modtronix-com/esp32MX-E/images/esp32mx-e_with_proto_db_back.jpg

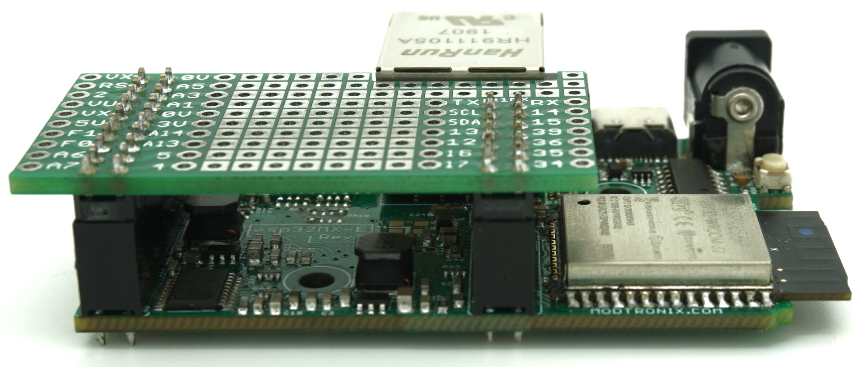
images/esp32mx-e_with_proto_db_back.jpg
