modtronix-com/esp32MX-E/images/esp32mx-e_with_proto_db_front.jpg

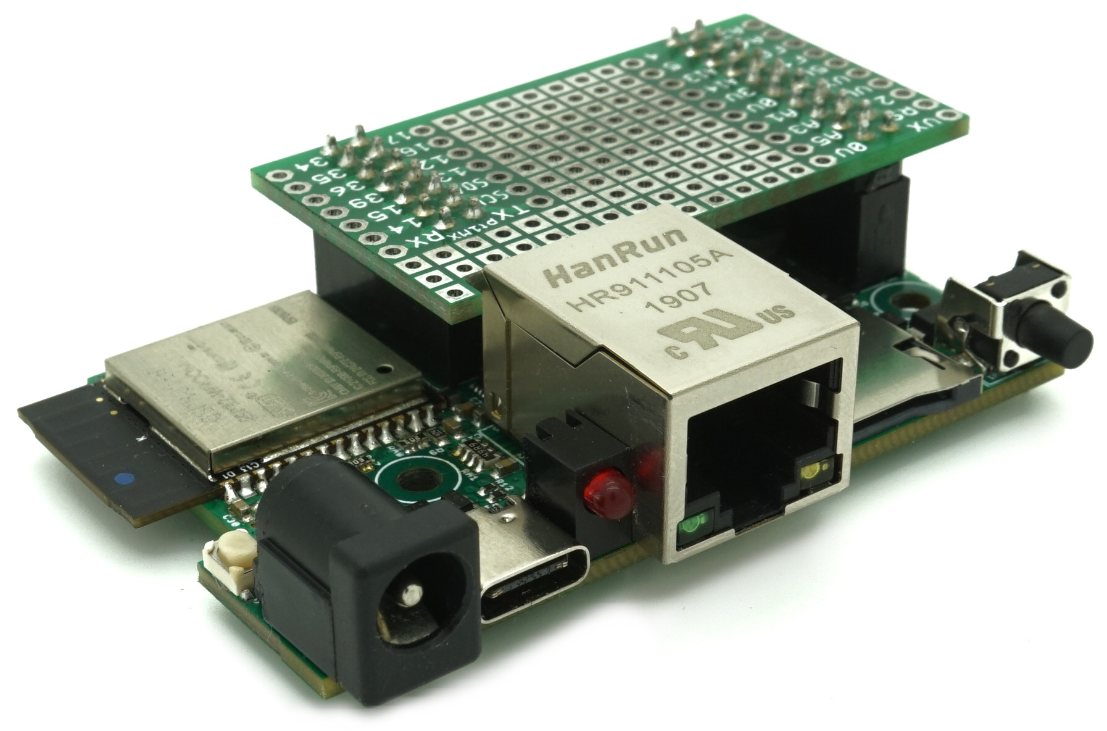
images/esp32mx-e_with_proto_db_front.jpg
