modtronix-com/esp32MX-E/pcb/pt1mx/pt1mx_schematics.png

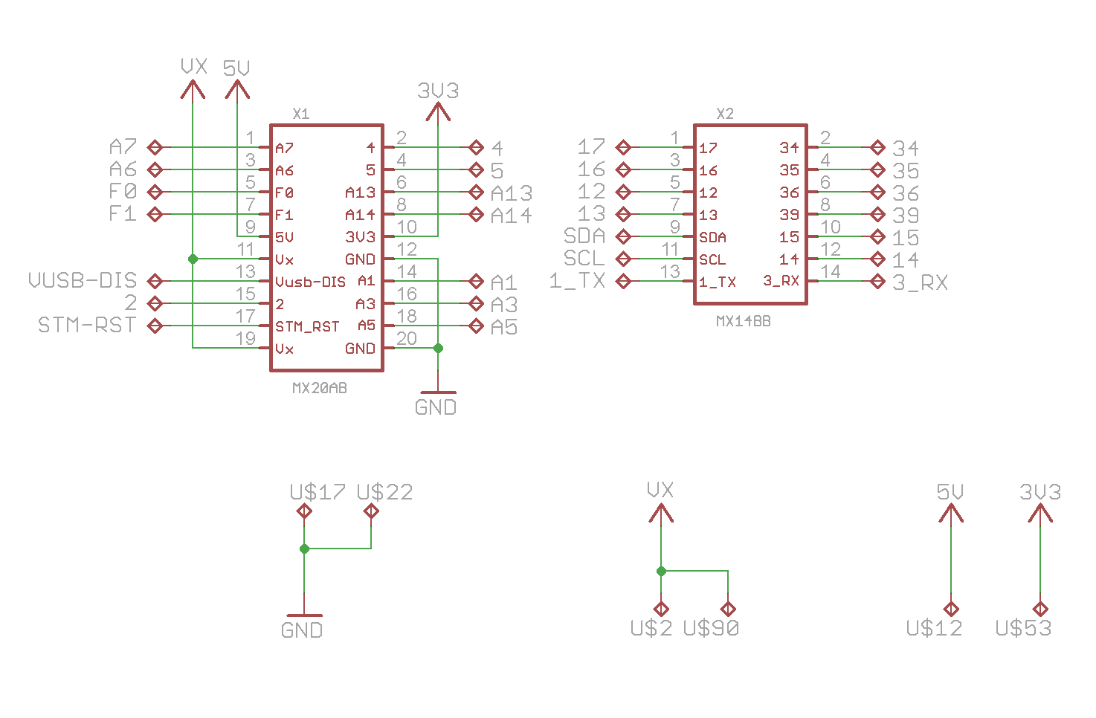
pcb/pt1mx/pt1mx_schematics.png
