modtronix-com/esp32MX-E/examples/idf/ethernet/main/main.c

/* ethernet Example

   This example code is in the Public Domain (or CC0 licensed, at your option.)

   Unless required by applicable law or agreed to in writing, this
   software is distributed on an "AS IS" BASIS, WITHOUT WARRANTIES OR
   CONDITIONS OF ANY KIND, either express or implied.
*/
#include <stdio.h>
#include <string.h>
#include "freertos/FreeRTOS.h"
#include "freertos/task.h"
#include "driver/gpio.h"
#include "tcpip_adapter.h"
#include "esp_eth.h"
#include "esp_event.h"
#include "esp_log.h"
#include "sdkconfig.h"


///////////////////////////////////////////////////////////////////////////////
// Defines
///////////////////////////////////////////////////////////////////////////////

#define BLINK_GPIO 5	// esp32MX-E uses GPIO 5 for the LED
// TODO: Chage to use CONFIG_ESP32MX_LED_GPIO as set by menuconfig

// Used when DHCP server is disabled
#define IP_DEFAULT_ADDRESS		"10.1.0.240"
#define IP_DEFAULT_NETMASK      "255.255.255.0"
#define IP_DEFAULT_GATEWAY      "10.1.0.254"

static const char *TAG = "eth_example";

/** Event handler for Ethernet events */
static void eth_event_handler(void *arg, esp_event_base_t event_base, int32_t event_id, void *event_data)
{
    uint8_t mac_addr[6] = {0};
    /* we can get the ethernet driver handle from event data */
    esp_eth_handle_t eth_handle = *(esp_eth_handle_t *)event_data;

    switch (event_id) {
    case ETHERNET_EVENT_CONNECTED:
        esp_eth_ioctl(eth_handle, ETH_CMD_G_MAC_ADDR, mac_addr);
        ESP_LOGI(TAG, "Ethernet Link Up");
        ESP_LOGI(TAG, "Ethernet HW Addr %02x:%02x:%02x:%02x:%02x:%02x",
                 mac_addr[0], mac_addr[1], mac_addr[2], mac_addr[3], mac_addr[4], mac_addr[5]);
        break;
    case ETHERNET_EVENT_DISCONNECTED:
        ESP_LOGI(TAG, "Ethernet Link Down");
        break;
    case ETHERNET_EVENT_START:
        ESP_LOGI(TAG, "Ethernet Started");
        break;
    case ETHERNET_EVENT_STOP:
        ESP_LOGI(TAG, "Ethernet Stopped");
        break;
    default:
        break;
    }
}

/** Event handler for IP_EVENT_ETH_GOT_IP */
static void got_ip_event_handler(void *arg, esp_event_base_t event_base, int32_t event_id, void *event_data)
{
    ip_event_got_ip_t *event = (ip_event_got_ip_t *) event_data;
    const tcpip_adapter_ip_info_t *ip_info = &event->ip_info;

    ESP_LOGI(TAG, "Ethernet Got IP Address");
    ESP_LOGI(TAG, "~~~~~~~~~~~");
    ESP_LOGI(TAG, "ETHIP:" IPSTR, IP2STR(&ip_info->ip));
    ESP_LOGI(TAG, "ETHMASK:" IPSTR, IP2STR(&ip_info->netmask));
    ESP_LOGI(TAG, "ETHGW:" IPSTR, IP2STR(&ip_info->gw));
    ESP_LOGI(TAG, "~~~~~~~~~~~");
}


void blink_task(void *pvParameter)
{
    gpio_pad_select_gpio(BLINK_GPIO);
    /* Set the GPIO as a push/pull output */
    gpio_set_direction(BLINK_GPIO, GPIO_MODE_OUTPUT);
    while(1) {
        /* Blink off (output low) */
        gpio_set_level(BLINK_GPIO, 0);
        vTaskDelay(120 / portTICK_PERIOD_MS);
        /* Blink on (output high) */
        gpio_set_level(BLINK_GPIO, 1);
        vTaskDelay(100 / portTICK_PERIOD_MS);
    }
}


void app_main() {

    tcpip_adapter_init();
	
    // Set static IP address, disable DHCP
#if(0)
    tcpip_adapter_ip_info_t ipInfo;
    tcpip_adapter_dhcpc_stop(TCPIP_ADAPTER_IF_ETH); // Don't run a DHCP client
    ip4addr_aton(IP_DEFAULT_ADDRESS, &ipInfo.ip);
    ip4addr_aton(IP_DEFAULT_GATEWAY, &ipInfo.gw);
    ip4addr_aton(IP_DEFAULT_NETMASK, &ipInfo.netmask);
    ESP_ERROR_CHECK(tcpip_adapter_set_ip_info(TCPIP_ADAPTER_IF_ETH, &ipInfo));
#endif

    ESP_ERROR_CHECK(esp_event_loop_create_default());
    ESP_ERROR_CHECK(tcpip_adapter_set_default_eth_handlers());
    ESP_ERROR_CHECK(esp_event_handler_register(ETH_EVENT, ESP_EVENT_ANY_ID, &eth_event_handler, NULL));
    ESP_ERROR_CHECK(esp_event_handler_register(IP_EVENT, IP_EVENT_ETH_GOT_IP, &got_ip_event_handler, NULL));

    eth_mac_config_t mac_config = ETH_MAC_DEFAULT_CONFIG();
    eth_phy_config_t phy_config = ETH_PHY_DEFAULT_CONFIG();

	phy_config.phy_addr = 0;	        // The PHY (LAN8720) on the esp32MX-E uses address 0
    phy_config.reset_gpio_num = -1;     // The GPIO number used to reset PHY chip, set to -1 to disable
    mac_config.smi_mdc_gpio_num = 23;   // Set the GPIO number used by SMI MDC
    mac_config.smi_mdio_gpio_num = 18;  // Set the GPIO number used by SMI MDIO
    esp_eth_mac_t *mac = esp_eth_mac_new_esp32(&mac_config);
    esp_eth_phy_t *phy = esp_eth_phy_new_lan8720(&phy_config);
    
    esp_eth_config_t config = ETH_DEFAULT_CONFIG(mac, phy);
    esp_eth_handle_t eth_handle = NULL;
    ESP_ERROR_CHECK(esp_eth_driver_install(&config, &eth_handle));
    ESP_ERROR_CHECK(esp_eth_start(eth_handle));

    // Blink LED
    gpio_pad_select_gpio(BLINK_GPIO);
    gpio_set_direction(BLINK_GPIO, GPIO_MODE_OUTPUT);
    while(1) {
        /* Blink off (output low) */
        gpio_set_level(BLINK_GPIO, 0);
        vTaskDelay(250 / portTICK_PERIOD_MS);
        /* Blink on (output high) */
        gpio_set_level(BLINK_GPIO, 1);
        vTaskDelay(500 / portTICK_PERIOD_MS);
    }
}
